teisenbe/transpsoe/hardware/transpsoe-spice.asc

D1: schottky; SS24
D2: schottky; SS24
D3: diode; 1N4148
J1: signal; ""
J2: signal; ""
R1: res; {mc(100k,tolb)}; tol=0.1
R2: res; {mc(100k,tolb)}; tol=0.1
R3: res; {mc(100k,tolb)}; tol=0.1
R4: res; 1Meg
R5: res; {mc(100k,tolb)}; tol=0.1
R6: res; {mc(100k,tolb)}; tol=0.1
R7: res; 50
R8: res; {mc(100k,tolb)}; tol=0.1
R9: res; {mc(100k,tolb)}; tol=0.1
R10: res; 50
R11: res; {mc(100k,tolb)}; tol=0.1
R12: res; {mc(100k,tolb)}
R13: res; {mc(100k,tolb)}
R14: res; 22k
R15: res; 950
R16: res; 39k
R17: res; {mc(10k,tola)}; tol=0.05
R18: res; {mc(100k,tolb)}; tol=0.1
R19: res; {mc(100k,tolb)}; tol=0.1
R20: res; {mc(10k,tola)}; tol=0.05
R21: res; {mc(10k,tola)}; tol=0.05
R22: res; {mc(10k,tola)}; tol=0.05
R23: res; {mc(10k,tola)}; tol=0.05
R24: res; {mc(30k,tola)}; tol=0.05
R25: res; {mc(110k, tolb)}
R26: res; {mc(10k,tolb)}
R27: res; {10k * (1 - (semitone_r_err - 1))}
R28: res; 100m
R29: res; R=if((time >= 0.05) & (time < 0.056),10G, semitone_r * semitone_r_err)
R30: res; {mc(820, tolb)}
R31: res; {mc(10k, tolb)}
R33: res; {mc(100k,tolb)}; tol=0.1
R34: res; {mc(100k,tolb)}; tol=0.1
R35: res; 50
R36: res; {mc(100k,tolb)}; tol=0.1
R37: res; {mc(100k,tolb)}
R38: res; {mc(100k,tolb)}; tol=0.1
R39: res; 50
R40: res; {mc(100k,tolb)}; tol=0.1
R41: res; {mc(100k,tolb)}
R42: res; {mc(100k,tolb)}; tol=0.1
R43: res; {mc(100k,tolb)}; tol=0.1
R44: res; {mc(100k,tolb)}; tol=0.1
R45: res; {mc(100k,tolb)}; tol=0.1
R46: res; 1Meg
R47: res; {mc(100k,tolb)}; tol=0.1
R48: res; {mc(100k,tolb)}; tol=0.1
R49: res; 50
R50: res; {mc(100k,tolb)}; tol=0.1
R51: res; {mc(100k,tolb)}; tol=0.1
R52: res; 50
R54: res; {mc(100k,tolb)}
R55: res; {mc(100k,tolb)}
R56: res; {mc(100k,tolb)}; tol=0.1
R57: res; {mc(100k,tolb)}; tol=0.1
R58: res; 50
R59: res; {mc(100k,tolb)}; tol=0.1
R60: res; {mc(100k,tolb)}
R61: res; {mc(100k,tolb)}; tol=0.1
R62: res; 50
R63: res; {mc(100k,tolb)}; tol=0.1
R64: res; {mc(100k,tolb)}
R65: res; {mc(100k,tolb)}; tol=0.1
R66: res; {mc(100k,tolb)}; tol=0.1
U1: OPA2991
U2: OPA2991
U3: OPA2991
U4: OPA2991
U5: OPA2991
U6: OPA2991
U7: OPA2991
U8: OPA2991
U9: OPA2991
U10: OPA2991
U11: OPA2991
U12: OPA2991
U13: OPA2991
U14: ADR5044
U15: OPA2991
U16: OPA2991
U17: OPA2991
U18: OPA2991
U19: OPA2991
U20: OPA2991
U21: OPA2991
V1: voltage; 12
V2: voltage; 12
V3: voltage; {tuned_v}
V4: voltage; SINE(2 7 500)
Named nets: 0, 12V, -12V, semiV, A+S, J3, J4, 1Vinv, -1Vinv, 2Vinv, 3Vinv, 4V, -3V, -2V, -1V, 1V, J8, J9, J5, J6, J10, J11
;.dc J1 -5 5 0.1 J2 -5 5 0.1
;.tran 0 0.2s 0s 0.001
;.step param run 1 10 1
.param tola=0.0005
.param tolb=0.001
.step param semitone_r list 1n 10k 20k 30k 40k 50k 60k 70k 80k 90k 100k 110k
.step param err_idx list 1 2 3
.param semitone_r_err=table(err_idx, 1, 0.999, 2, 1, 3, 1.001) tuned_v=table(err_idx, 1, -83.303m, 2, -83.223m, 3, -83m)
.tran 0 0.04s 0s 0.001
.meas expected_semi param floor(semitone_r / 10k)
.meas semitone_err AVG log10(abs(V(semiv)*12 - expected_semi))
